gilgen/shademaker/bin/auto_sensors.py

auto_sensors = {
    0 : {
        'blindNums' : [1,2,3,4,5,6,7,8,9],
        'GPIO' : 20
    },
    1 : {
        'blindNums' : [10,11,12],
        'GPIO' : 21
    },
    2 : {
        'blindNums' : [13,14,15],
        'GPIO' : 16
    }
}
