gilgen/shademaker/bin/auto_heartbeat.py

#!/usr/bin/env python

# This command runs via cron every minute
# * * * * * /home/pi/shademaker/bin/auto_heartbeat.py >> /home/pi/shademaker/log/auto_heartbeat.log 2>&1

from smbus2 import SMBus
import sys
import os
import json
import time
import datetime
from blind_addresses import blind_address_mappings
from auto_sensors import auto_sensors
from auto_states import auto_states
import RPi.GPIO as GPIO

AUTO_CMD_INTERVAL = 3600 * 5 # 5 hour no activity gap required for auto cmd
BLIND_COMMAND_FILE = os.path.join(sys.path[0], 'send_blind_command.py')
auto_states = {int(k):v for k,v in auto_states.items()}
GPIO.setmode(GPIO.BCM)

def light_sensor_low(sensor):
    pin = auto_sensors[sensor]['GPIO']
    GPIO.setup(pin, GPIO.IN)
    return GPIO.input(pin)

# For the log
print "\n-----  " + datetime.datetime.now().strftime("%Y-%m-%d %H:%M:%S") + "  ----"

# For each sensors in the list
#   If auto mode is enabled
#       If enough time has passed for a new command
#           If light sensor is high
#               Send UP to each blind in set
#           If light sensors is low
#               Send DOWN to each blind in set
for sensor in auto_sensors:
    if auto_states[sensor]["isEnabled"]:
        current_time = int(time.time())
        last_command_at = int(auto_states[sensor]["lastCommandAt"])
        if current_time - last_command_at > AUTO_CMD_INTERVAL:
            cmd = 100
            if light_sensor_low(sensor):
                cmd = 0
            blindNums = ','.join(map(str, auto_sensors[sensor]['blindNums']))
            cmd = '{} {} {}'.format(BLIND_COMMAND_FILE, blindNums, cmd)
            print "Sensor {}: Sending auto command: {}".format(sensor, cmd)
            os.system(cmd)
        else:
            print "Sensor {}: Not enough time has passed since last auto command".format(sensor)
    else:
        print "Sensor {}: Not enabled right now".format(sensor)
