gilgen/shademaker/bin/blind_addresses.py

blind_address_mappings = {
  1  : 0b00011,
  2  : 0b00100,
  3  : 0b00101,
  4  : 0b00110,
  5  : 0b00111,
  6  : 0b01000,
  7  : 0b01001,
  8  : 0b01010,
  9  : 0b01011,
  10 : 0b01100,
  11 : 0b01101,
  12 : 0b01110,
  13 : 0b01111,
  14 : 0b10000,
  15 : 0b10001
}
